Luunoronti/tercet-audio/riaa/riaa_preamp.kicad_sch

## KiCad design riaa/riaa_preamp.kicad_sch (2026-08-25)

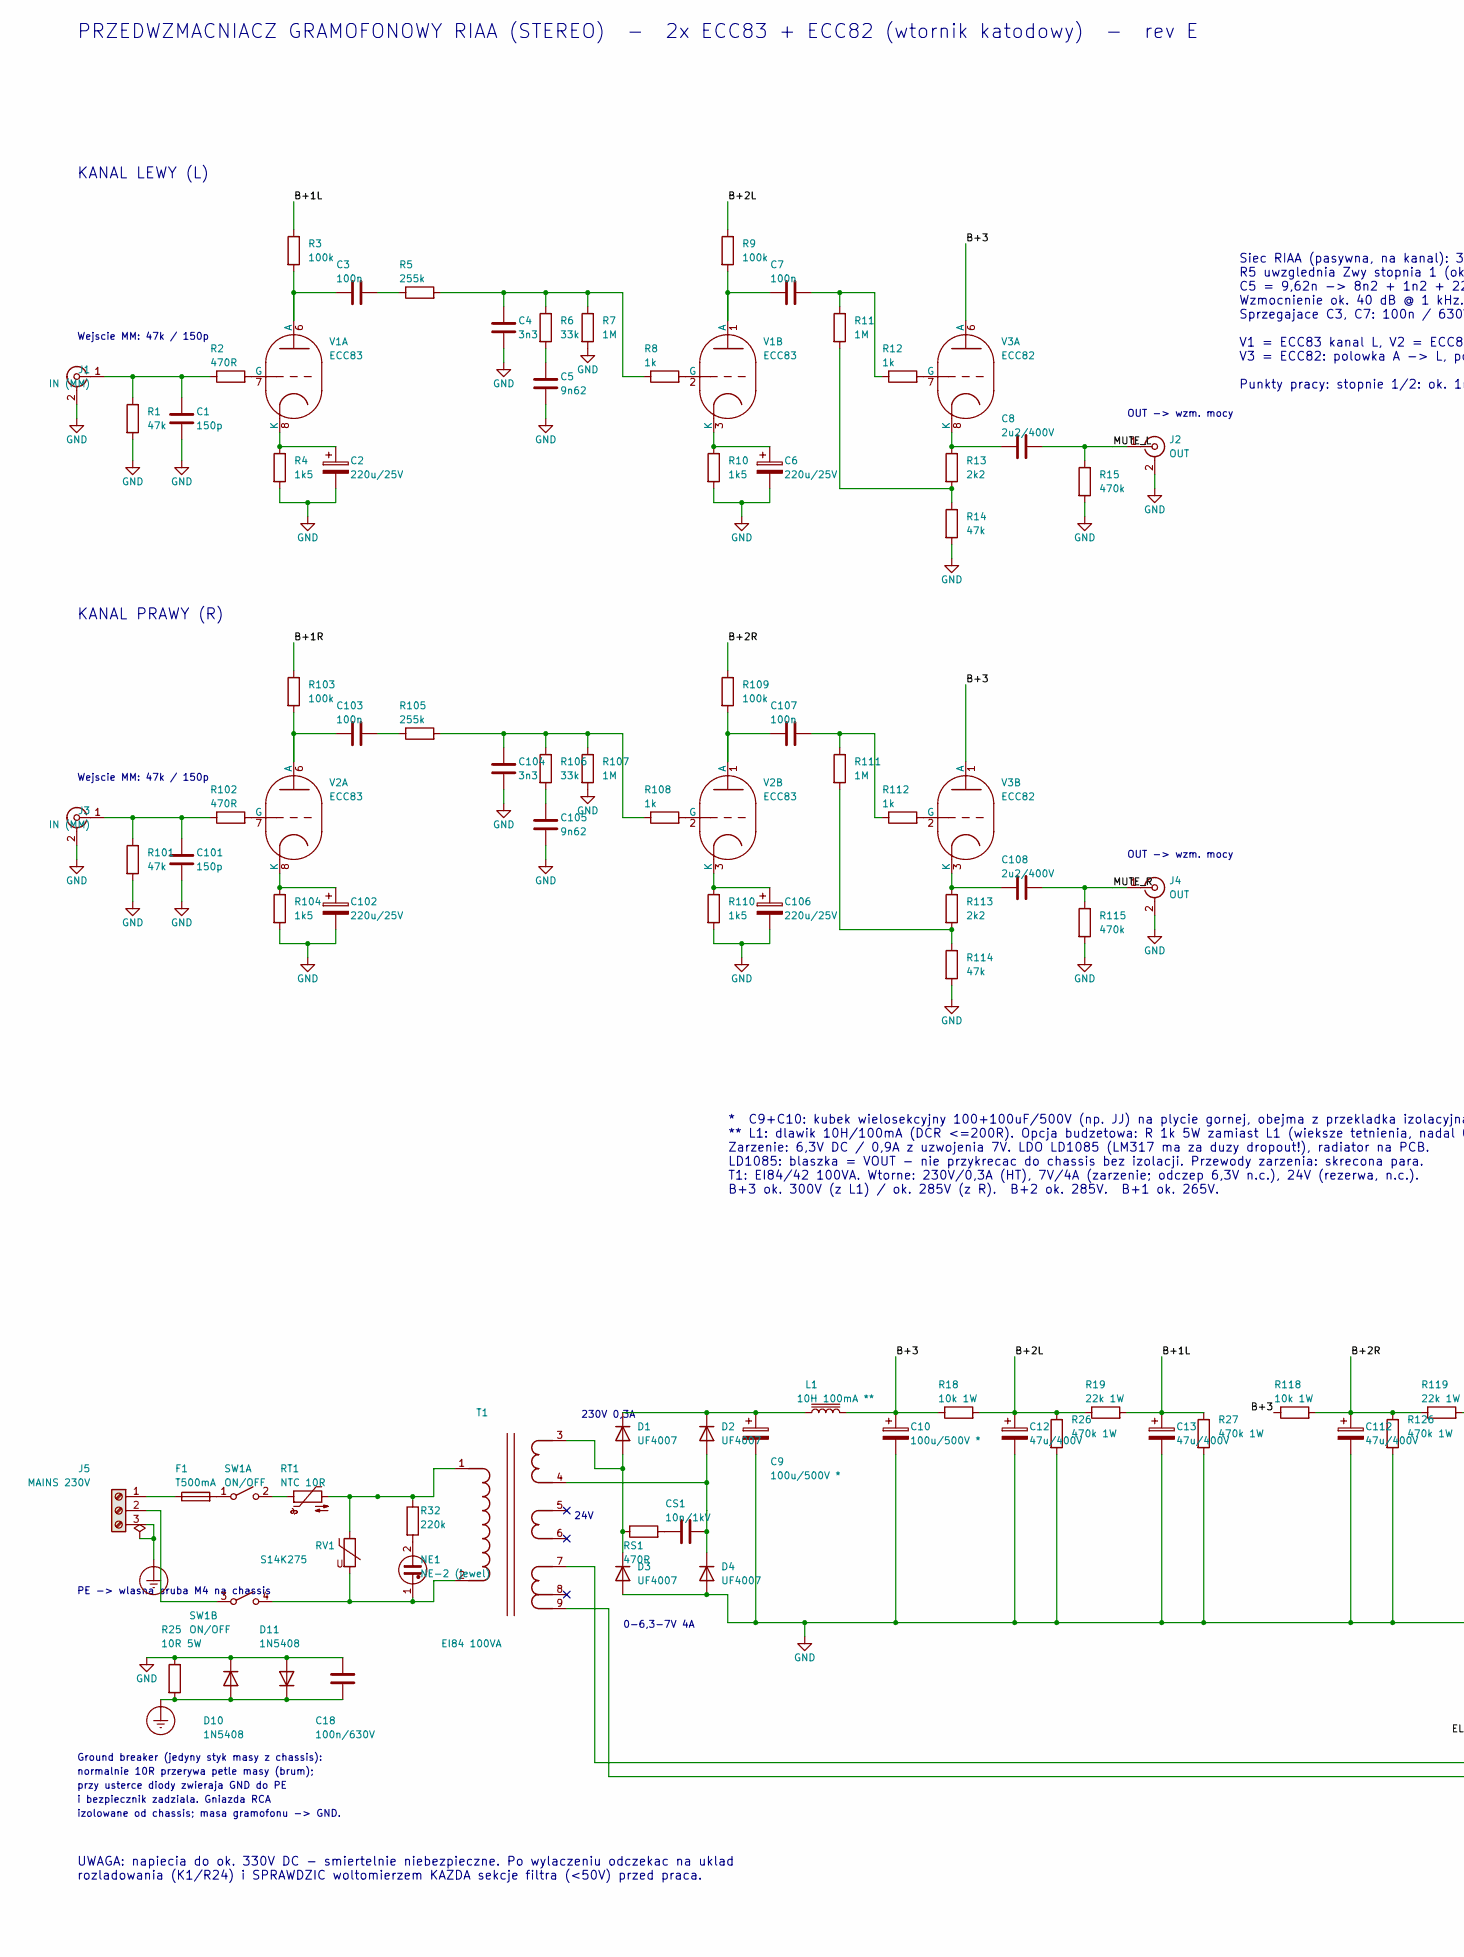
[picture p7: schematic riaa_preamp.kicad_sch, part in row 1, column 1]

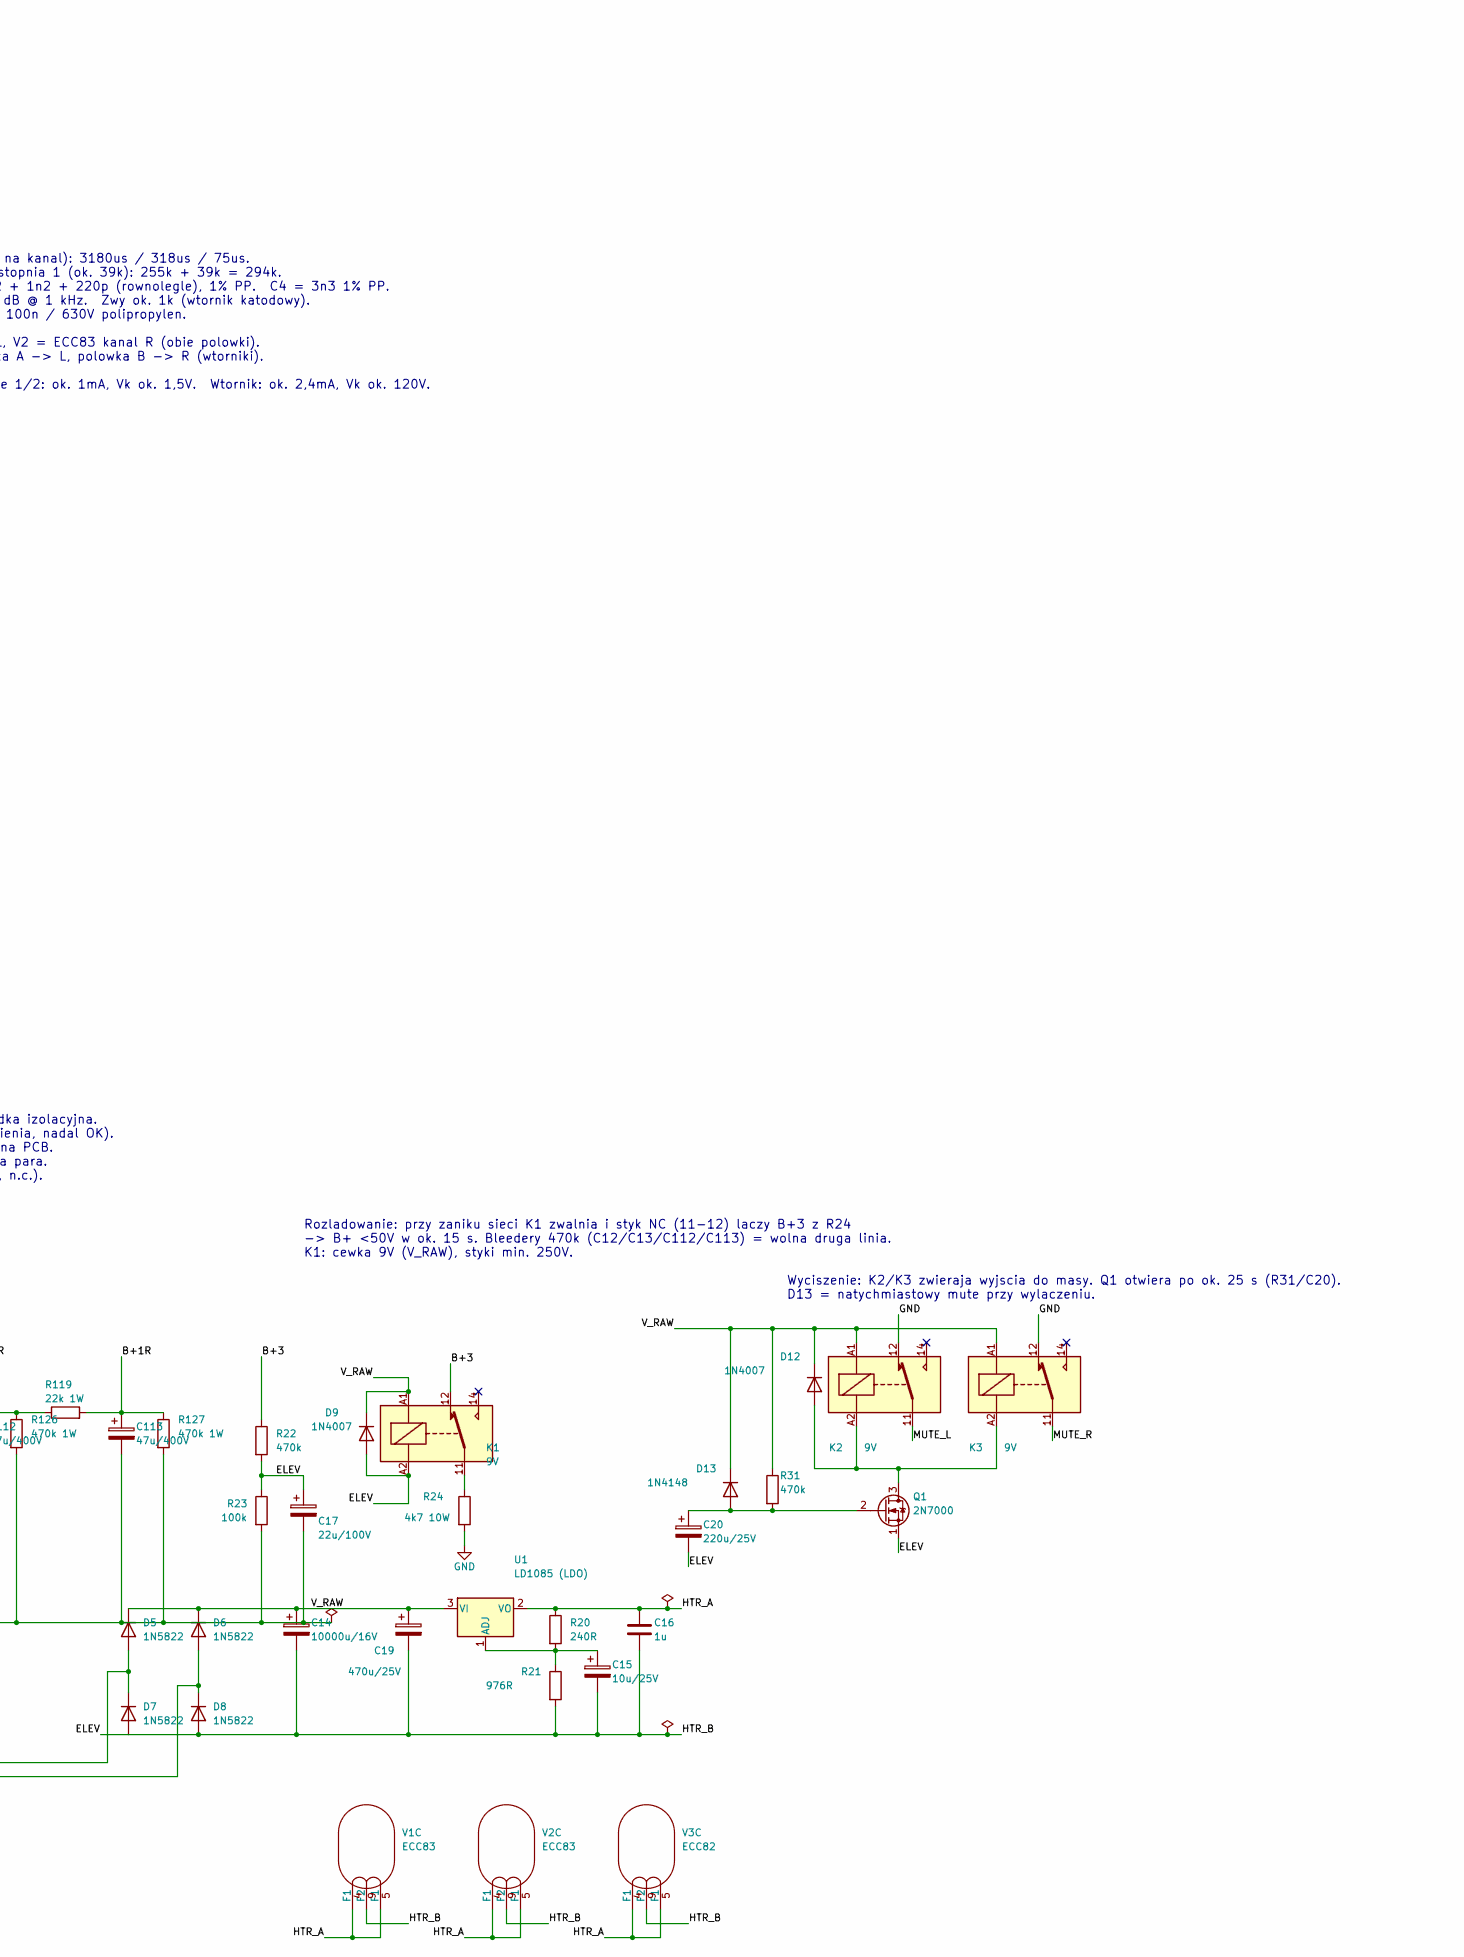
[picture p8: schematic riaa_preamp.kicad_sch, part in row 1, column 2]

Parts:
C1, C101: 150p
C2, C6, C20, C102, C106: 220u/25V
C3, C7, C103, C107: 100n
C4, C104: 3n3
C5, C105: 9n62
C8, C108: 2u2/400V
C9, C10: 100u/500V *
C12, C13, C112, C113: 47u/400V
C14: 10000u/16V
C15: 10u/25V
C16: 1u
C17: 22u/100V
C18: 100n/630V
C19: 470u/25V
CS1: 10n/1kV
D1, D2, D3, D4: UF4007
D5, D6, D7, D8: 1N5822
D9, D12: 1N4007
D10, D11: 1N5408
D13: 1N4148
F1: T500mA
J1, J3: IN (MM)
J2, J4: OUT
J5: MAINS 230V
K1, K2, K3: 9V
L1: 10H 100mA **
NE1: NE-2 (jewel)
Q1: 2N7000
R1, R14, R101, R114: 47k
R2, R102: 470R
R3, R9, R23, R103, R109: 100k
R4, R10, R104, R110: 1k5
R5, R105: 255k
R6, R106: 33k
R7, R11, R107, R111: 1M
R8, R12, R108, R112: 1k
R13, R113: 2k2
R15, R22, R31, R115: 470k
R18, R118: 10k 1W
R19, R119: 22k 1W
R20: 240R
R21: 976R
R24: 4k7 10W
R25: 10R 5W
R26, R27, R126, R127: 470k 1W
R32: 220k
RS1: 470R
RT1: NTC 10R
RV1: S14K275
SW1: ON/OFF
T1: EI84 100VA
U1: LD1085 (LDO)
V1, V2: ECC83
V3: ECC82

Connections:
B+1L: C13.1, R3.1, R19.2, R27.1
B+1R: C113.1, R103.1, R119.2, R127.1
B+2L: C12.1, R9.1, R18.2, R19.1, R26.1
B+2R: C112.1, R109.1, R118.2, R119.1, R126.1
B+3: C10.1, K1.12, L1.2, R18.1, R22.1, R118.1, V3.1 (A), V3.6 (A)
ELEV: C14.2, C15.2, C16.2, C17.1, C19.2, C20.2, D7.2 (A), D8.2 (A), D9.2 (A), K1.A2, Q1.1 (S), R21.2, R22.2, R23.1, V1.9 (F2), V2.9 (F2), V3.9 (F2)
Earth_Protective: C18.2, D10.2 (A), D11.1 (K), J5.3, R25.2
GND: C1.2, C2.2, C4.2, C5.2, C6.2, C9.2, C10.2, C12.2, C13.2, C17.2, C18.1, C101.2, C102.2, C104.2, C105.2, C106.2, C112.2, C113.2, D3.2 (A), D4.2 (A), D10.1 (K), D11.2 (A), J1.2 (Ext), J2.2 (Ext), J3.2 (Ext), J4.2 (Ext), K2.12, K3.12, R1.2, R4.2, R7.2, R10.2, R14.2, R15.2, R23.2, R24.2, R25.1, R26.2, R27.2, R101.2, R104.2, R107.2, R110.2, R114.2, R115.2, R126.2, R127.2
HTR_A: C16.1, R20.1, U1.2 (VO), V1.4 (F1), V1.5 (F1), V2.4 (F1), V2.5 (F1), V3.4 (F1), V3.5 (F1)
MUTE_L: C8.2, J2.1 (In), K2.11, R15.1
MUTE_R: C108.2, J4.1 (In), K3.11, R115.1
unnamed: C1.1, J1.1 (In), R1.1, R2.1
unnamed: C2.1, R4.1, V1.8 (K)
unnamed: C3.1, R3.2, V1.6 (A)
unnamed: C3.2, R5.1
unnamed: C4.1, R5.2, R6.1, R7.1, R8.1
unnamed: C5.1, R6.2
unnamed: C6.1, R10.1, V1.3 (K)
unnamed: C7.1, R9.2, V1.1 (A)
unnamed: C7.2, R11.1, R12.1
unnamed: C8.1, R13.1, V3.8 (K)
unnamed: C9.1, D1.1 (K), D2.1 (K), L1.1
unnamed: C15.1, R20.2, R21.1, U1.1 (ADJ)
unnamed: C20.1, D13.2 (A), Q1.2 (G), R31.2
unnamed: C101.1, J3.1 (In), R101.1, R102.1
unnamed: C102.1, R104.1, V2.8 (K)
unnamed: C103.1, R103.2, V2.6 (A)
unnamed: C103.2, R105.1
unnamed: C104.1, R105.2, R106.1, R107.1, R108.1
unnamed: C105.1, R106.2
unnamed: C106.1, R110.1, V2.3 (K)
unnamed: C107.1, R109.2, V2.1 (A)
unnamed: C107.2, R111.1, R112.1
unnamed: C108.1, R113.1, V3.3 (K)
unnamed: CS1.1, RS1.2
unnamed: CS1.2, D2.2 (A), D4.1 (K), T1.4
unnamed: D1.2 (A), D3.1 (K), RS1.1, T1.3
unnamed: D5.2 (A), D7.1 (K), T1.7
unnamed: D6.2 (A), D8.1 (K), T1.9
unnamed: D12.2 (A), K2.A2, K3.A2, Q1.3 (D)
unnamed: F1.1, J5.1
unnamed: F1.2, SW1.1 (A)
unnamed: J5.2, SW1.3 (A)
unnamed: K1.11, R24.1
unnamed: NE1.1, RV1.2, SW1.4 (B), T1.2
unnamed: NE1.2, R32.2
unnamed: R2.2, V1.7 (G)
unnamed: R8.2, V1.2 (G)
unnamed: R11.2, R13.2, R14.1
unnamed: R12.2, V3.7 (G)
unnamed: R32.1, RT1.2, RV1.1, T1.1
unnamed: R102.2, V2.7 (G)
unnamed: R108.2, V2.2 (G)
unnamed: R111.2, R113.2, R114.1
unnamed: R112.2, V3.2 (G)
unnamed: RT1.1, SW1.2 (B)
V_RAW: C14.1, C19.1, D5.1 (K), D6.1 (K), D9.1 (K), D12.1 (K), D13.1 (K), K1.A1, K2.A1, K3.A1, R31.1, U1.3 (VI)

Notes on the sheet:
KANAL LEWY (L)
Wejscie MM: 47k / 150p
OUT -> wzm. mocy
KANAL PRAWY (R)
Siec RIAA (pasywna, na kanal): 3180us / 318us / 75us.
R5 uwzglednia Zwy stopnia 1 (ok. 39k): 255k + 39k = 294k.
C5 = 9,62n -> 8n2 + 1n2 + 220p (rownolegle), 1% PP. C4 = 3n3 1% PP.
Wzmocnienie ok. 40 dB @ 1 kHz. Zwy ok. 1k (wtornik katodowy).
Sprzegajace C3, C7: 100n / 630V polipropylen.
V1 = ECC83 kanal L, V2 = ECC83 kanal R (obie polowki).
V3 = ECC82: polowka A -> L, polowka B -> R (wtorniki).
Punkty pracy: stopnie 1/2: ok. 1mA, Vk ok. 1,5V. Wtornik: ok. 2,4mA, Vk ok. 120V.
PE -> wlasna sruba M4 na chassis
230V 0,3A
24V
0-6,3-7V 4A
Rozladowanie: przy zaniku sieci K1 zwalnia i styk NC (11-12) laczy B+3 z R24
-> B+ <50V w ok. 15 s. Bleedery 470k (C12/C13/C112/C113) = wolna druga linia.
K1: cewka 9V (V_RAW), styki min. 250V.
Wyciszenie: K2/K3 zwieraja wyjscia do masy. Q1 otwiera po ok. 25 s (R31/C20).
D13 = natychmiastowy mute przy wylaczeniu.
Ground breaker (jedyny styk masy z chassis):
normalnie 10R przerywa petle masy (brum);
przy usterce diody zwieraja GND do PE
i bezpiecznik zadziala. Gniazda RCA
izolowane od chassis; masa gramofonu -> GND.
PRZEDWZMACNIACZ GRAMOFONOWY RIAA (STEREO) - 2x ECC83 + ECC82 (wtornik katodowy) - rev E
* C9+C10: kubek wielosekcyjny 100+100uF/500V (np. JJ) na plycie gornej, obejma z przekladka izolacyjna.
** L1: dlawik 10H/100mA (DCR <=200R). Opcja budzetowa: R 1k 5W zamiast L1 (wieksze tetnienia, nadal OK).
Zarzenie: 6,3V DC / 0,9A z uzwojenia 7V. LDO LD1085 (LM317 ma za duzy dropout!), radiator na PCB.
LD1085: blaszka = VOUT - nie przykrecac do chassis bez izolacji. Przewody zarzenia: skrecona para.
T1: EI84/42 100VA. Wtorne: 230V/0,3A (HT), 7V/4A (zarzenie; odczep 6,3V n.c.), 24V (rezerwa, n.c.).
B+3 ok. 300V (z L1) / ok. 285V (z R). B+2 ok. 285V. B+1 ok. 265V.
UWAGA: napiecia do ok. 330V DC - smiertelnie niebezpieczne. Po wylaczeniu odczekac na uklad
rozladowania (K1/R24) i SPRAWDZIC woltomierzem KAZDA sekcje filtra (<50V) przed praca.
