Luunoronti/tercet-audio/riaa/riaa_preamp_purist.kicad_sch

## KiCad design riaa/riaa_preamp_purist.kicad_sch (2026-08-26)

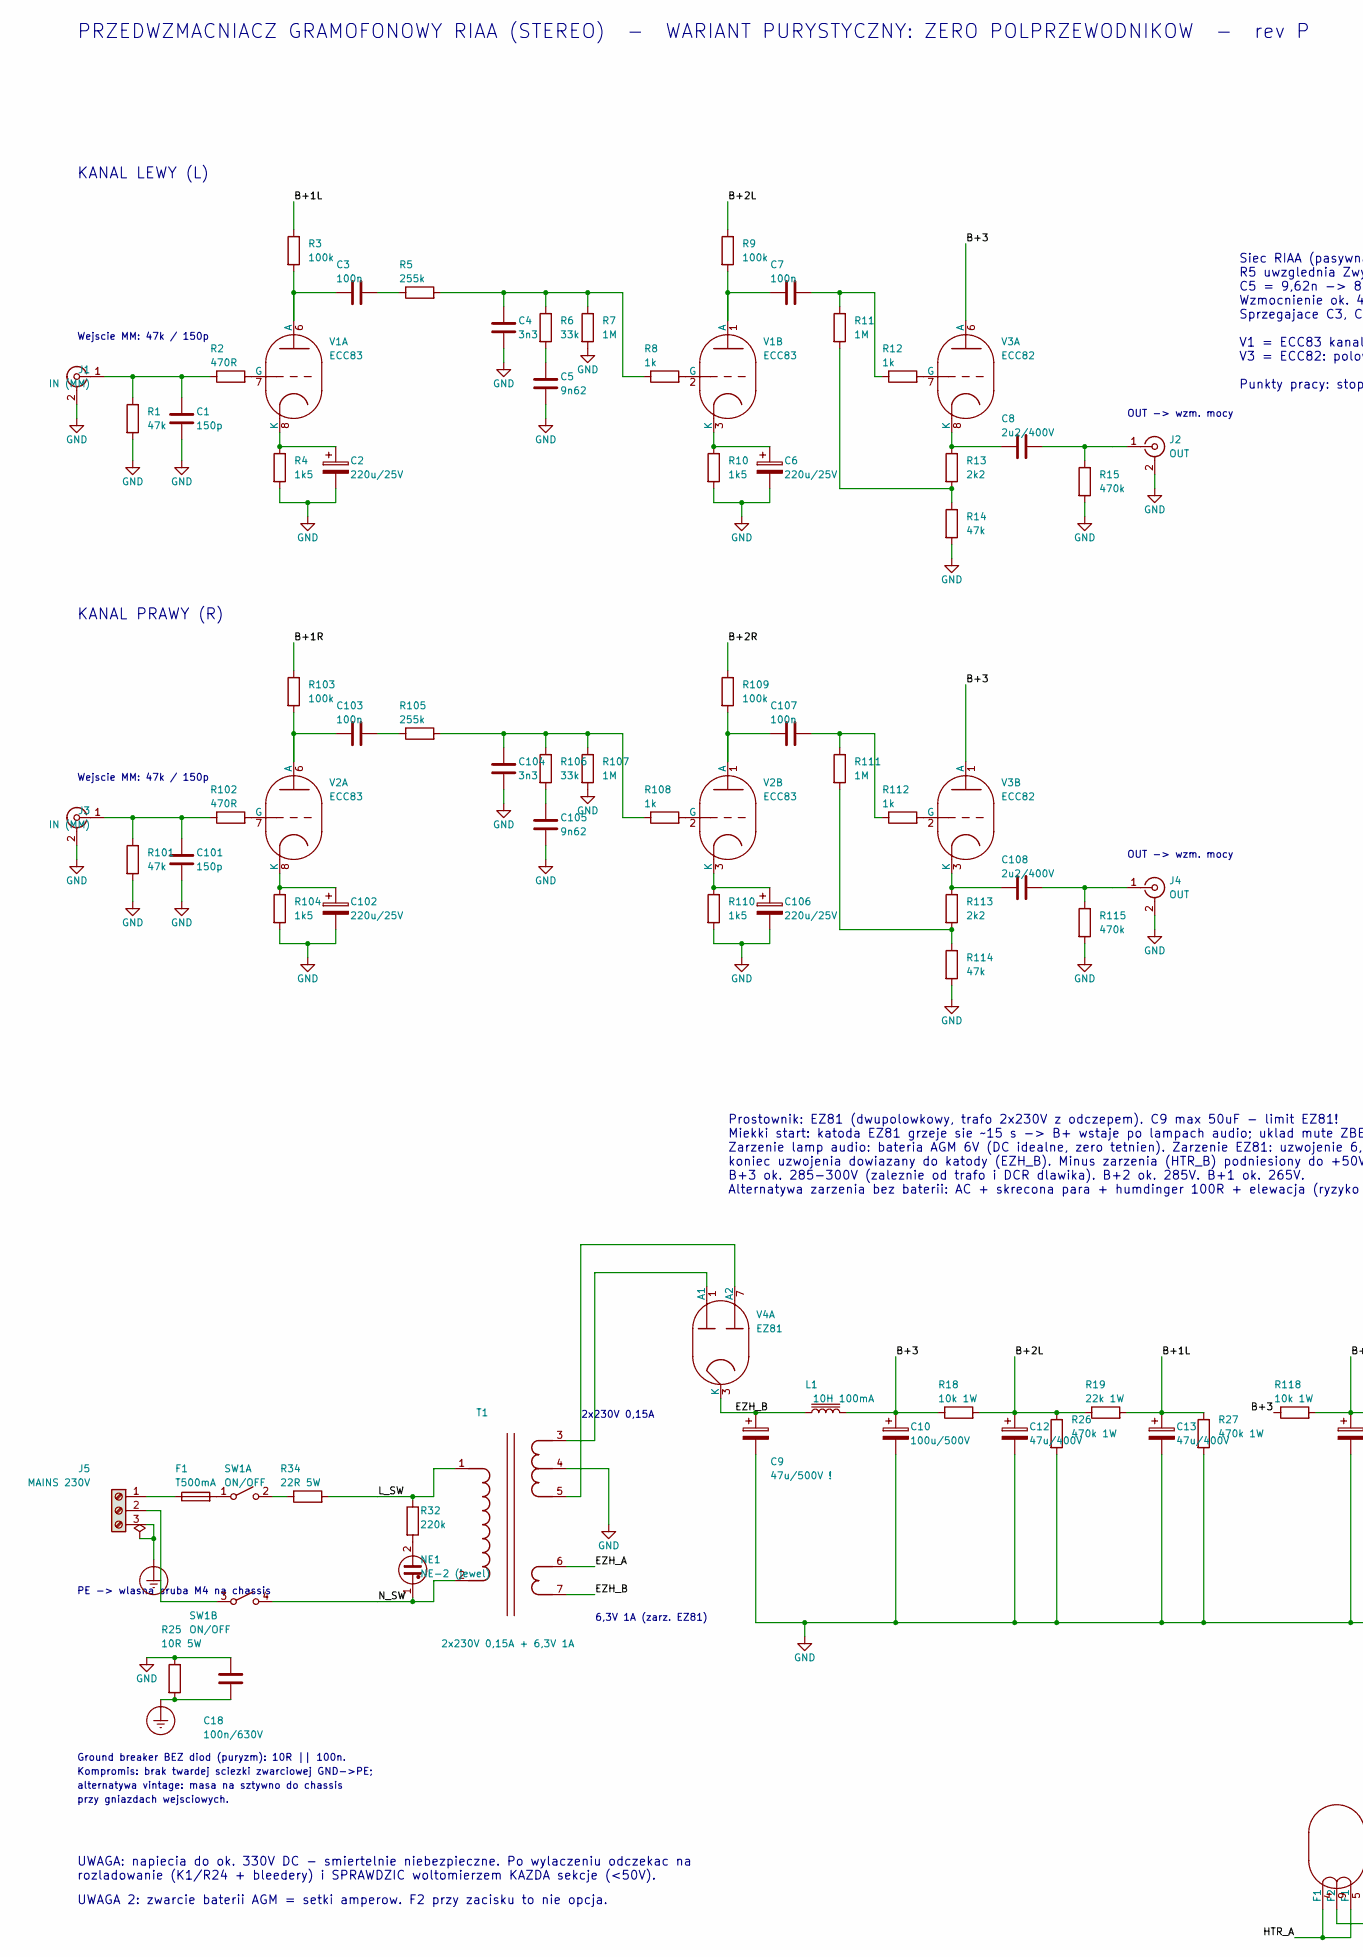
[picture p9: schematic riaa_preamp_purist.kicad_sch, part in row 1, column 1]

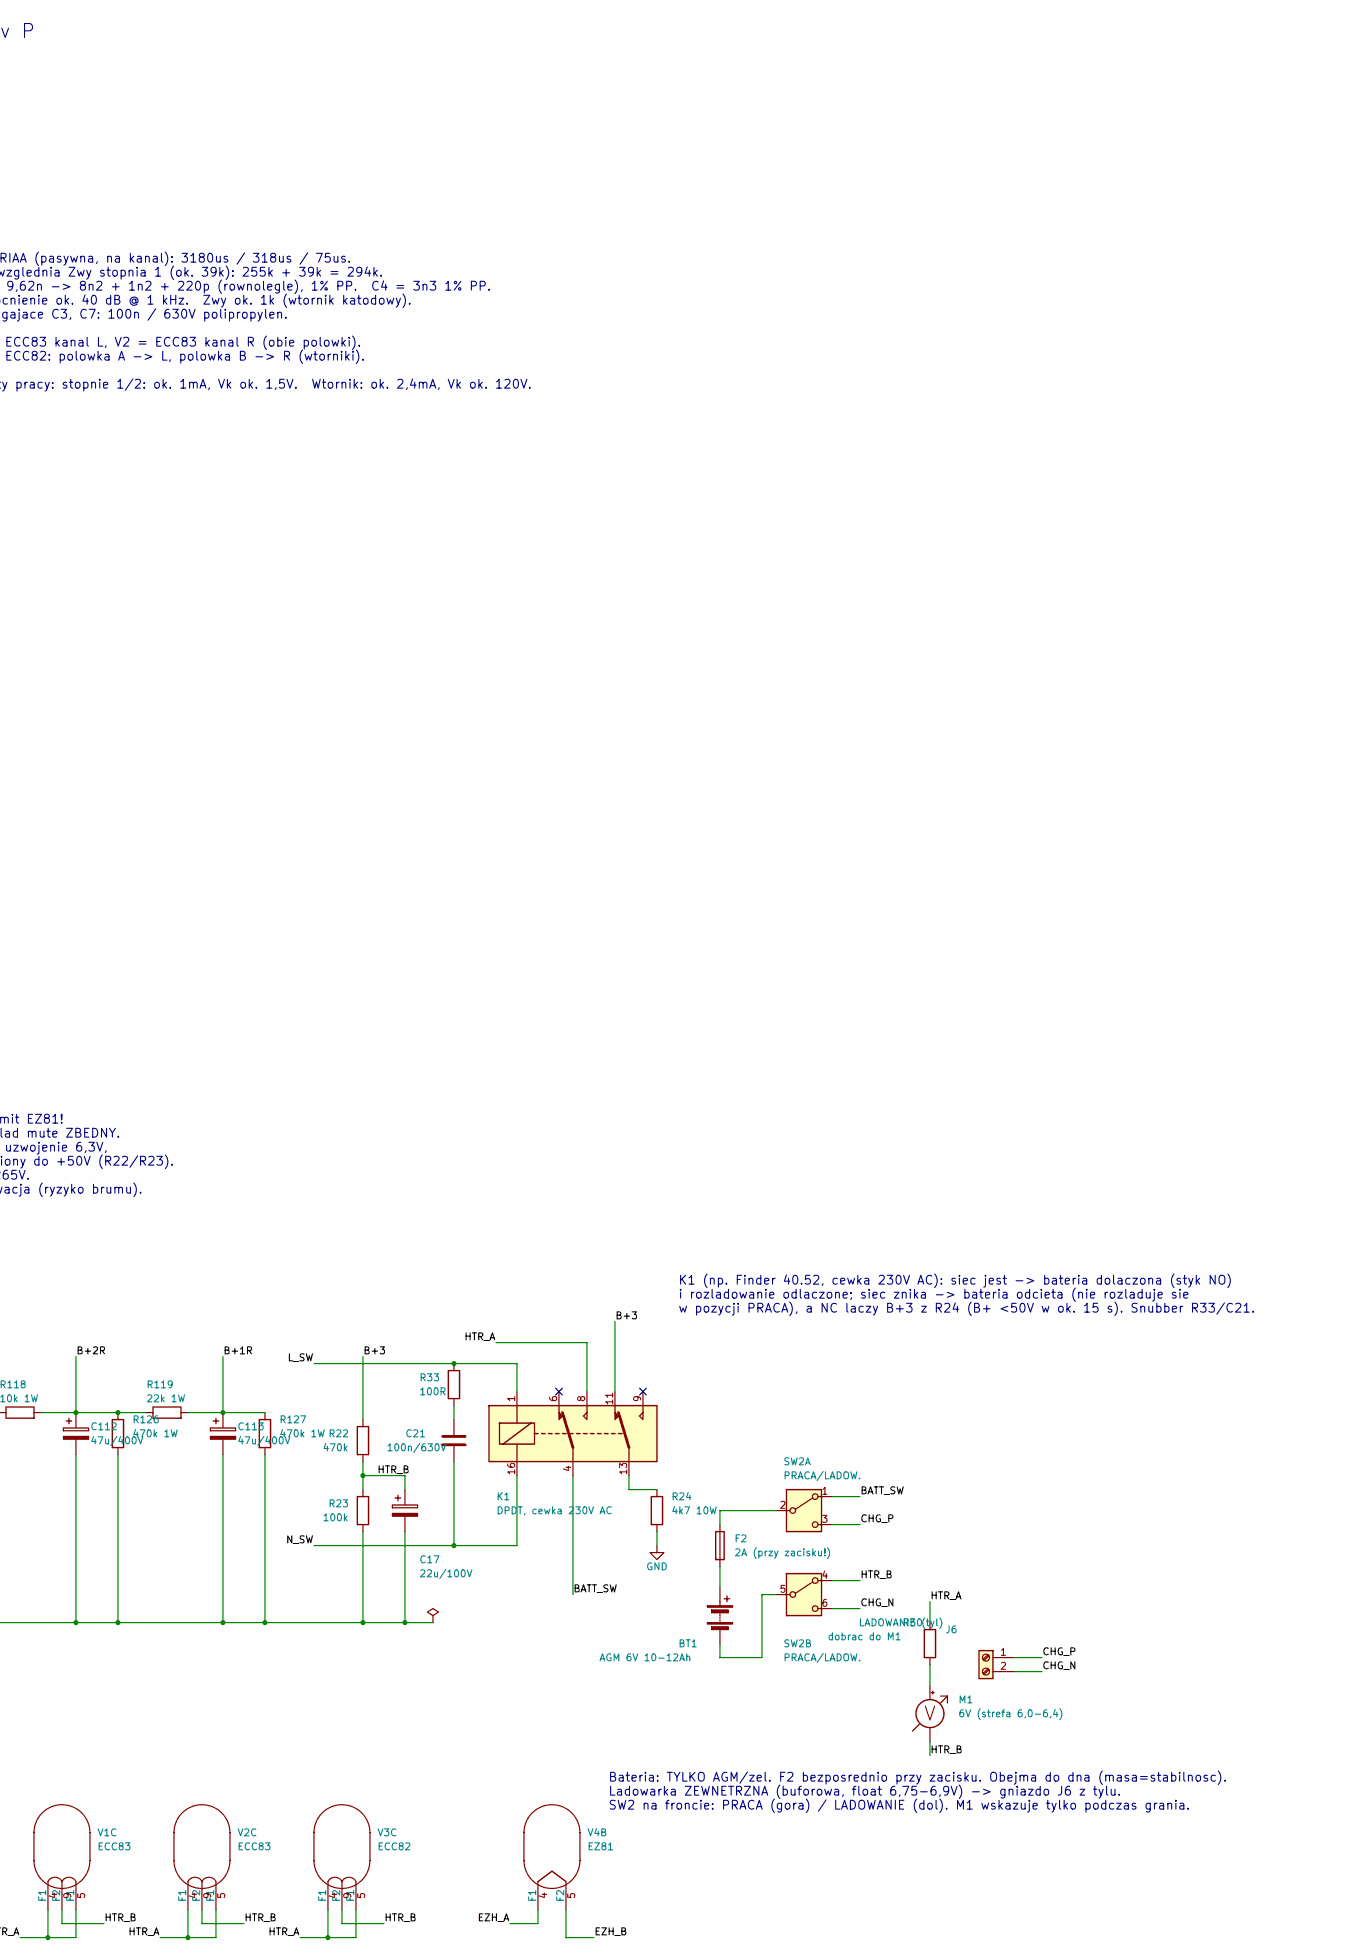
[picture p10: schematic riaa_preamp_purist.kicad_sch, part in row 1, column 2]

Parts:
BT1: AGM 6V 10-12Ah
C1, C101: 150p
C2, C6, C102, C106: 220u/25V
C3, C7, C103, C107: 100n
C4, C104: 3n3
C5, C105: 9n62
C8, C108: 2u2/400V
C9: 47u/500V !
C10: 100u/500V
C12, C13, C112, C113: 47u/400V
C17: 22u/100V
C18, C21: 100n/630V
F1: T500mA
F2: 2A (przy zacisku!)
J1, J3: IN (MM)
J2, J4: OUT
J5: MAINS 230V
J6: LADOWANIE (tyl)
K1: DPDT, cewka 230V AC
L1: 10H 100mA
M1: 6V (strefa 6,0-6,4)
NE1: NE-2 (jewel)
R1, R14, R101, R114: 47k
R2, R102: 470R
R3, R9, R23, R103, R109: 100k
R4, R10, R104, R110: 1k5
R5, R105: 255k
R6, R106: 33k
R7, R11, R107, R111: 1M
R8, R12, R108, R112: 1k
R13, R113: 2k2
R15, R22, R115: 470k
R18, R118: 10k 1W
R19, R119: 22k 1W
R24: 4k7 10W
R25: 10R 5W
R26, R27, R126, R127: 470k 1W
R30: dobrac do M1
R32: 220k
R33: 100R
R34: 22R 5W
SW1: ON/OFF
SW2: PRACA/LADOW.
T1: 2x230V 0,15A + 6,3V 1A
V1, V2: ECC83
V3: ECC82
V4: EZ81

Connections:
B+1L: C13.1, R3.1, R19.2, R27.1
B+1R: C113.1, R103.1, R119.2, R127.1
B+2L: C12.1, R9.1, R18.2, R19.1, R26.1
B+2R: C112.1, R109.1, R118.2, R119.1, R126.1
B+3: C10.1, K1.11, L1.2, R18.1, R22.1, R118.1, V3.1 (A), V3.6 (A)
BATT_SW: K1.4, SW2.1 (A)
CHG_N: J6.2, SW2.6 (C)
CHG_P: J6.1, SW2.3 (C)
EZH_A: T1.6, V4.4 (F1)
EZH_B: C9.1, L1.1, T1.7, V4.3 (K), V4.5 (F2)
Earth_Protective: C18.2, J5.3, R25.2
GND: C1.2, C2.2, C4.2, C5.2, C6.2, C9.2, C10.2, C12.2, C13.2, C17.2, C18.1, C101.2, C102.2, C104.2, C105.2, C106.2, C112.2, C113.2, J1.2 (Ext), J2.2 (Ext), J3.2 (Ext), J4.2 (Ext), R1.2, R4.2, R7.2, R10.2, R14.2, R15.2, R23.2, R24.2, R25.1, R26.2, R27.2, R101.2, R104.2, R107.2, R110.2, R114.2, R115.2, R126.2, R127.2, T1.4
HTR_A: K1.8, R30.1, V1.4 (F1), V1.5 (F1), V2.4 (F1), V2.5 (F1), V3.4 (F1), V3.5 (F1)
HTR_B: C17.1, M1.1 (-), R22.2, R23.1, SW2.4 (A), V1.9 (F2), V2.9 (F2), V3.9 (F2)
L_SW: K1.1, R32.1, R33.1, R34.2, T1.1
N_SW: C21.2, K1.16, NE1.1, SW1.4 (B), T1.2
unnamed: BT1.1 (+), F2.2
unnamed: BT1.2 (-), SW2.5 (B)
unnamed: C1.1, J1.1 (In), R1.1, R2.1
unnamed: C2.1, R4.1, V1.8 (K)
unnamed: C3.1, R3.2, V1.6 (A)
unnamed: C3.2, R5.1
unnamed: C4.1, R5.2, R6.1, R7.1, R8.1
unnamed: C5.1, R6.2
unnamed: C6.1, R10.1, V1.3 (K)
unnamed: C7.1, R9.2, V1.1 (A)
unnamed: C7.2, R11.1, R12.1
unnamed: C8.1, R13.1, V3.8 (K)
unnamed: C8.2, J2.1 (In), R15.1
unnamed: C21.1, R33.2
unnamed: C101.1, J3.1 (In), R101.1, R102.1
unnamed: C102.1, R104.1, V2.8 (K)
unnamed: C103.1, R103.2, V2.6 (A)
unnamed: C103.2, R105.1
unnamed: C104.1, R105.2, R106.1, R107.1, R108.1
unnamed: C105.1, R106.2
unnamed: C106.1, R110.1, V2.3 (K)
unnamed: C107.1, R109.2, V2.1 (A)
unnamed: C107.2, R111.1, R112.1
unnamed: C108.1, R113.1, V3.3 (K)
unnamed: C108.2, J4.1 (In), R115.1
unnamed: F1.1, J5.1
unnamed: F1.2, SW1.1 (A)
unnamed: F2.1, SW2.2 (B)
unnamed: J5.2, SW1.3 (A)
unnamed: K1.13, R24.1
unnamed: M1.2 (+), R30.2
unnamed: NE1.2, R32.2
unnamed: R2.2, V1.7 (G)
unnamed: R8.2, V1.2 (G)
unnamed: R11.2, R13.2, R14.1
unnamed: R12.2, V3.7 (G)
unnamed: R34.1, SW1.2 (B)
unnamed: R102.2, V2.7 (G)
unnamed: R108.2, V2.2 (G)
unnamed: R111.2, R113.2, R114.1
unnamed: R112.2, V3.2 (G)
unnamed: T1.3, V4.1 (A1)
unnamed: T1.5, V4.7 (A2)

Notes on the sheet:
KANAL LEWY (L)
Wejscie MM: 47k / 150p
OUT -> wzm. mocy
KANAL PRAWY (R)
Siec RIAA (pasywna, na kanal): 3180us / 318us / 75us.
R5 uwzglednia Zwy stopnia 1 (ok. 39k): 255k + 39k = 294k.
C5 = 9,62n -> 8n2 + 1n2 + 220p (rownolegle), 1% PP. C4 = 3n3 1% PP.
Wzmocnienie ok. 40 dB @ 1 kHz. Zwy ok. 1k (wtornik katodowy).
Sprzegajace C3, C7: 100n / 630V polipropylen.
V1 = ECC83 kanal L, V2 = ECC83 kanal R (obie polowki).
V3 = ECC82: polowka A -> L, polowka B -> R (wtorniki).
Punkty pracy: stopnie 1/2: ok. 1mA, Vk ok. 1,5V. Wtornik: ok. 2,4mA, Vk ok. 120V.
PE -> wlasna sruba M4 na chassis
2x230V 0,15A
6,3V 1A (zarz. EZ81)
K1 (np. Finder 40.52, cewka 230V AC): siec jest -> bateria dolaczona (styk NO)
i rozladowanie odlaczone; siec znika -> bateria odcieta (nie rozladuje sie
w pozycji PRACA), a NC laczy B+3 z R24 (B+ <50V w ok. 15 s). Snubber R33/C21.
Bateria: TYLKO AGM/zel. F2 bezposrednio przy zacisku. Obejma do dna (masa=stabilnosc).
Ladowarka ZEWNETRZNA (buforowa, float 6,75-6,9V) -> gniazdo J6 z tylu.
SW2 na froncie: PRACA (gora) / LADOWANIE (dol). M1 wskazuje tylko podczas grania.
Ground breaker BEZ diod (puryzm): 10R || 100n.
Kompromis: brak twardej sciezki zwarciowej GND->PE;
alternatywa vintage: masa na sztywno do chassis
przy gniazdach wejsciowych.
PRZEDWZMACNIACZ GRAMOFONOWY RIAA (STEREO) - WARIANT PURYSTYCZNY: ZERO POLPRZEWODNIKOW - rev P
Prostownik: EZ81 (dwupolowkowy, trafo 2x230V z odczepem). C9 max 50uF - limit EZ81!
Miekki start: katoda EZ81 grzeje sie ~15 s -> B+ wstaje po lampach audio; uklad mute ZBEDNY.
Zarzenie lamp audio: bateria AGM 6V (DC idealne, zero tetnien). Zarzenie EZ81: uzwojenie 6,3V,
koniec uzwojenia dowiazany do katody (EZH_B). Minus zarzenia (HTR_B) podniesiony do +50V (R22/R23).
B+3 ok. 285-300V (zaleznie od trafo i DCR dlawika). B+2 ok. 285V. B+1 ok. 265V.
Alternatywa zarzenia bez baterii: AC + skrecona para + humdinger 100R + elewacja (ryzyko brumu).
UWAGA: napiecia do ok. 330V DC - smiertelnie niebezpieczne. Po wylaczeniu odczekac na
rozladowanie (K1/R24 + bleedery) i SPRAWDZIC woltomierzem KAZDA sekcje (<50V).
UWAGA 2: zwarcie baterii AGM = setki amperow. F2 przy zacisku to nie opcja.
