Luunoronti/tercet-audio/headamp/kicad/headamp.kicad_sch

## KiCad design headamp/kicad/headamp.kicad_sch (2026-09-08)

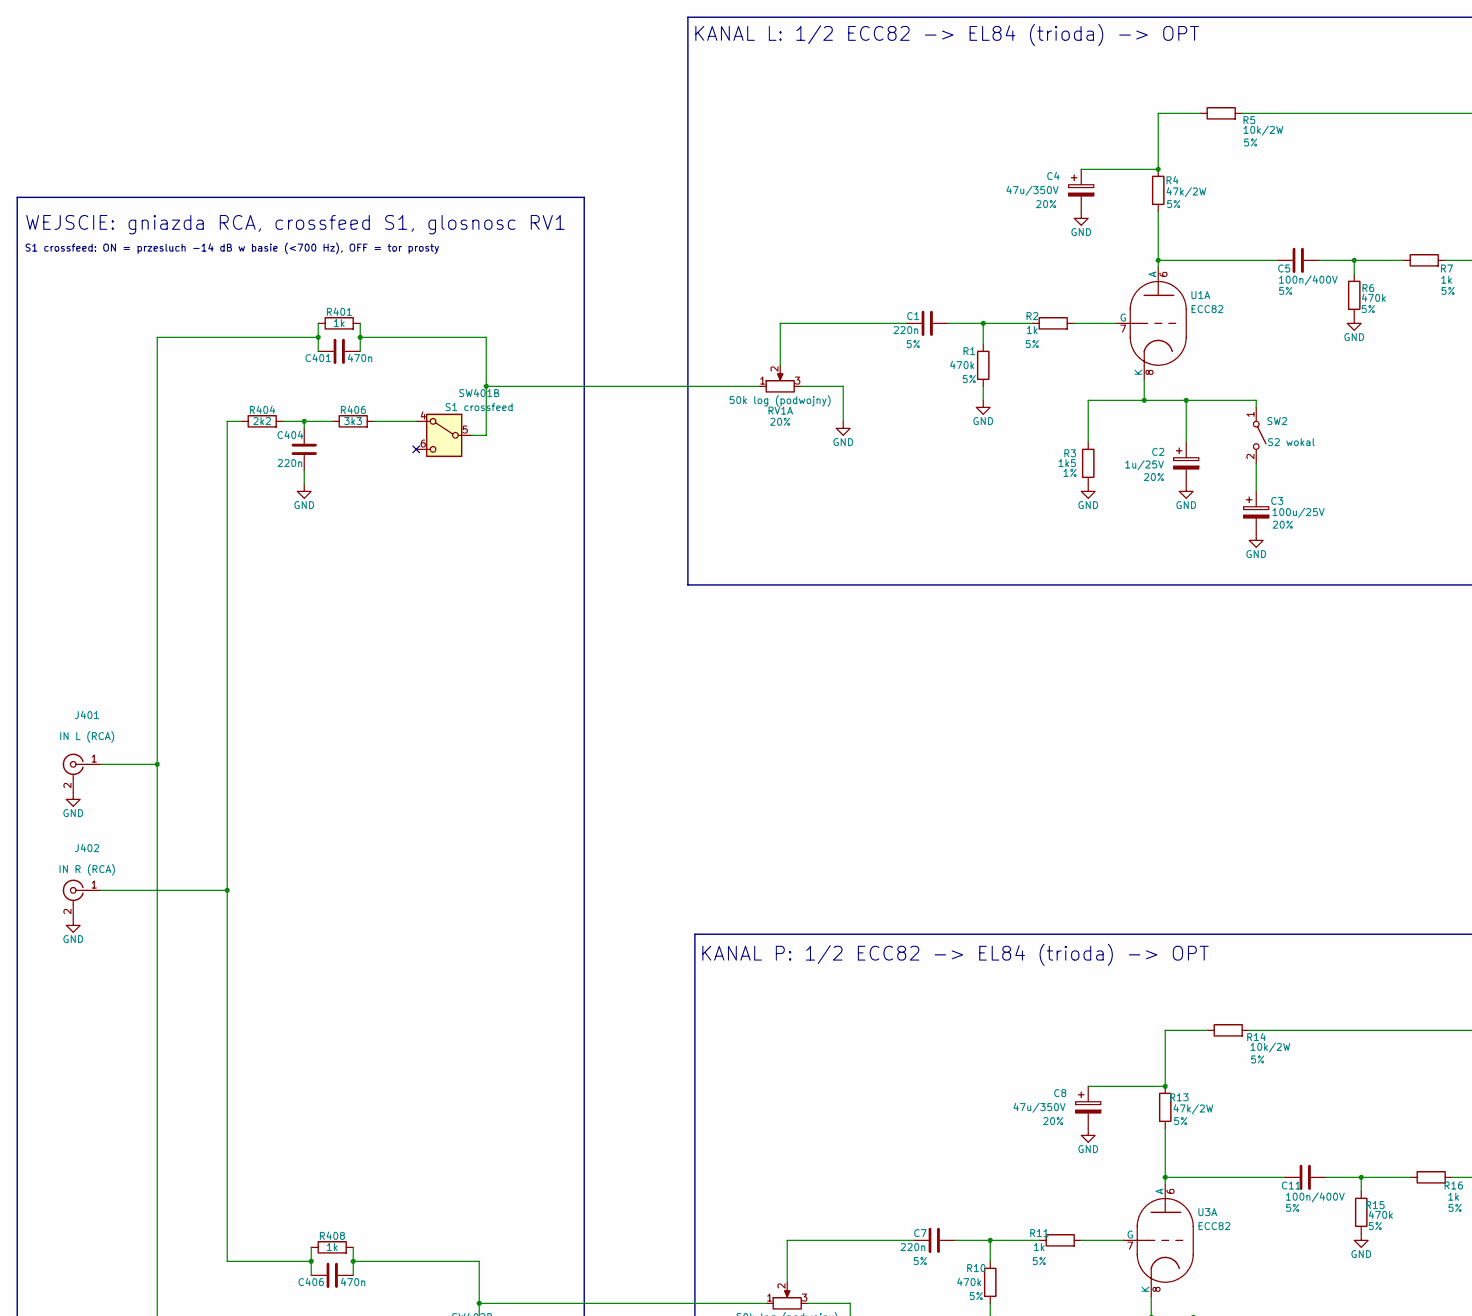
[picture p11: schematic headamp.kicad_sch, part in row 1, column 1]

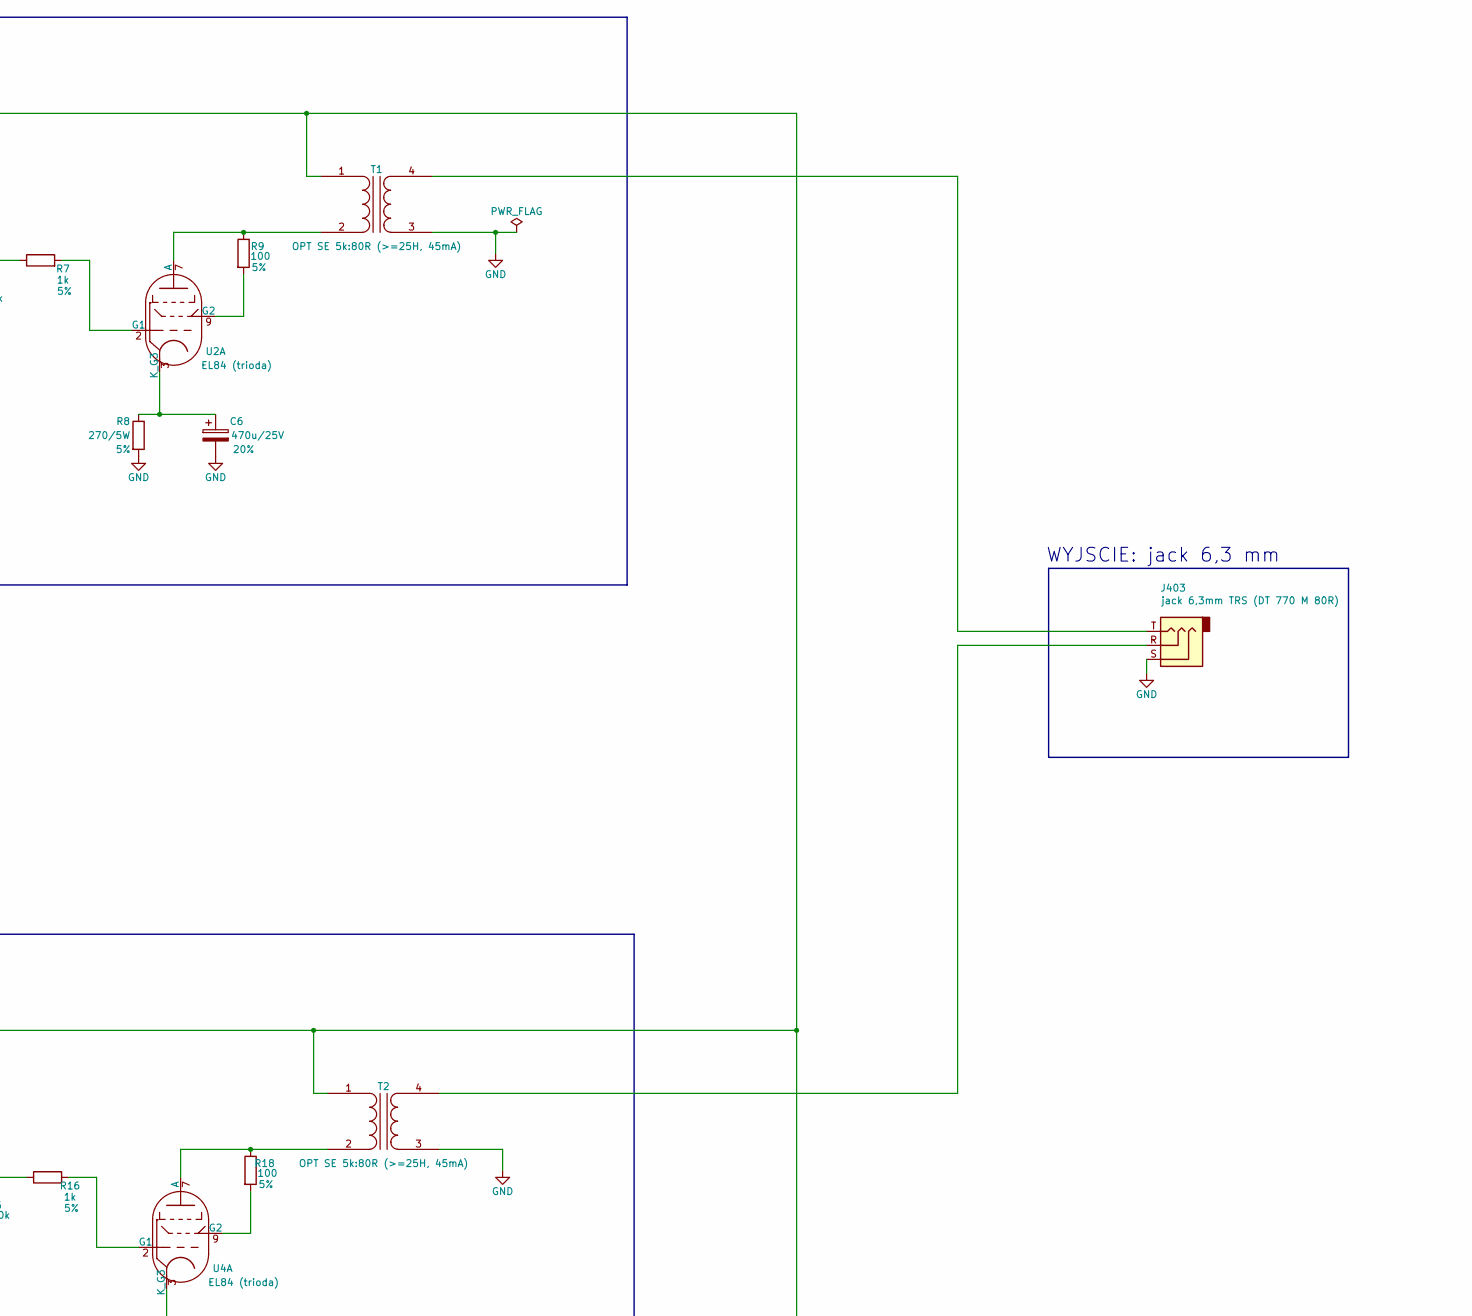
[picture p12: schematic headamp.kicad_sch, part in row 1, column 2]

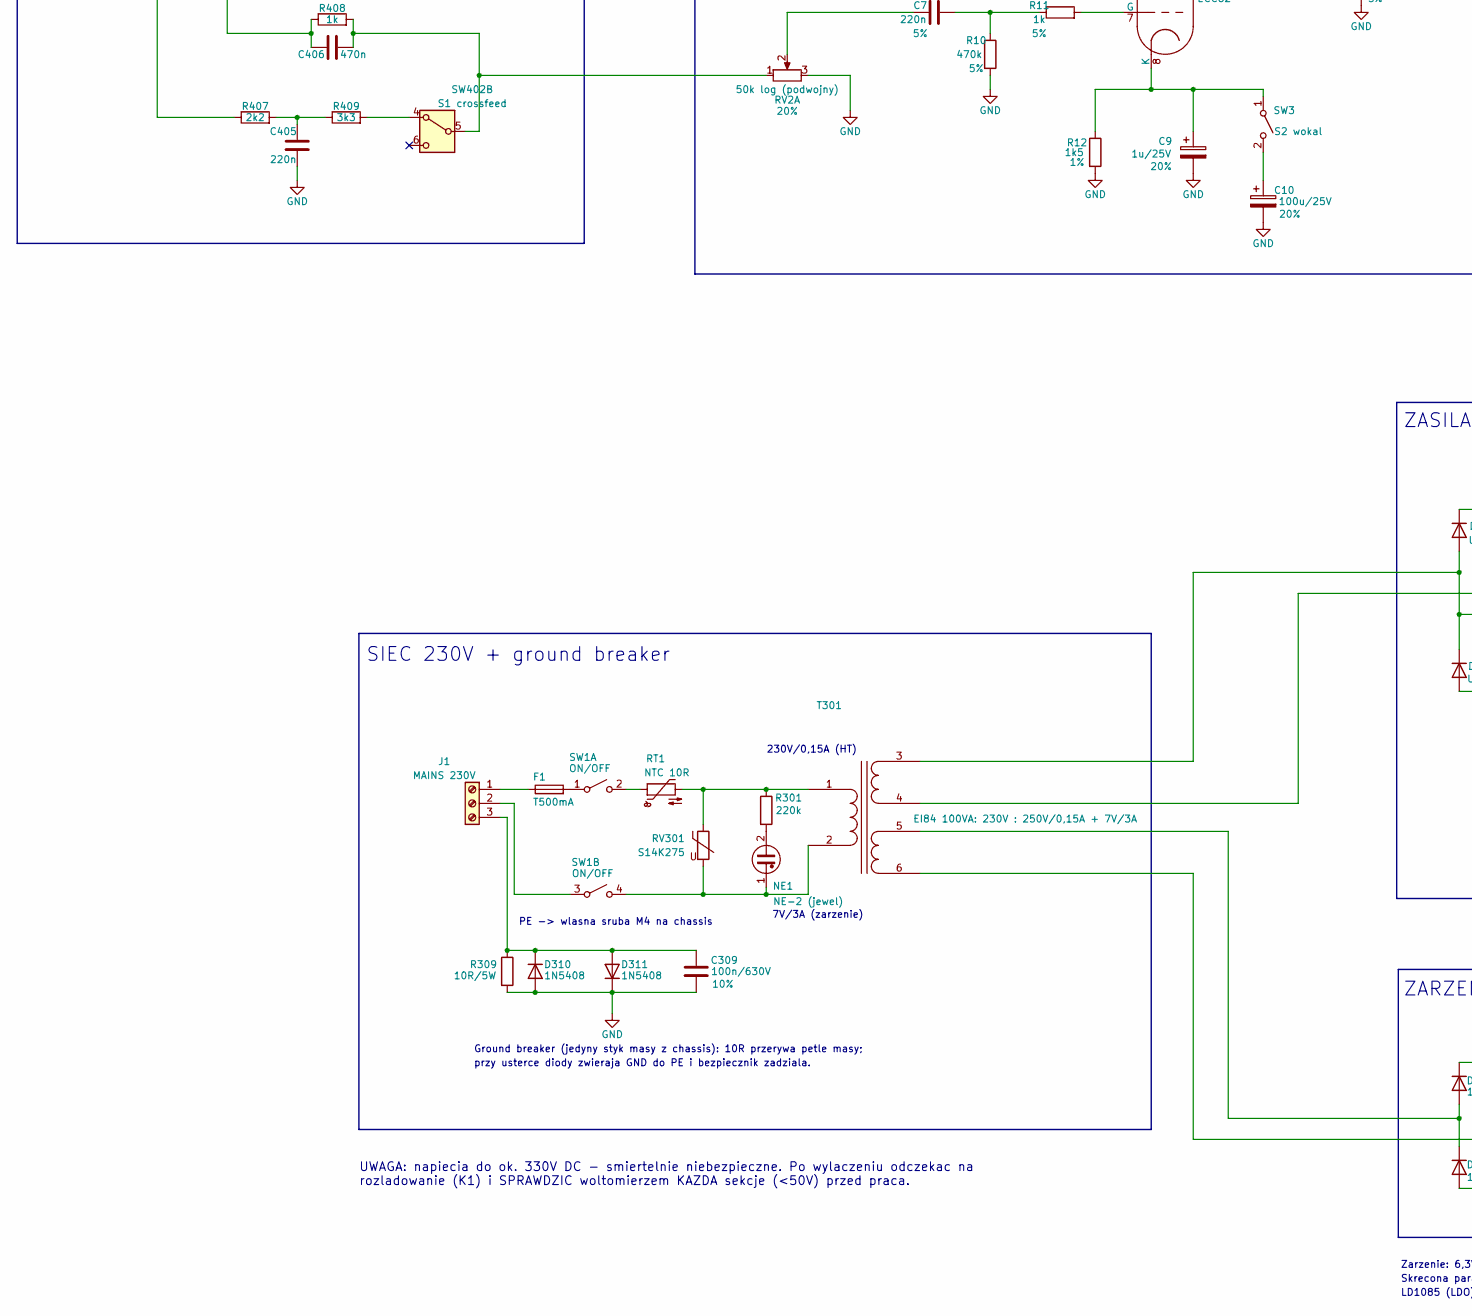
[picture p13: schematic headamp.kicad_sch, part in row 2, column 1]

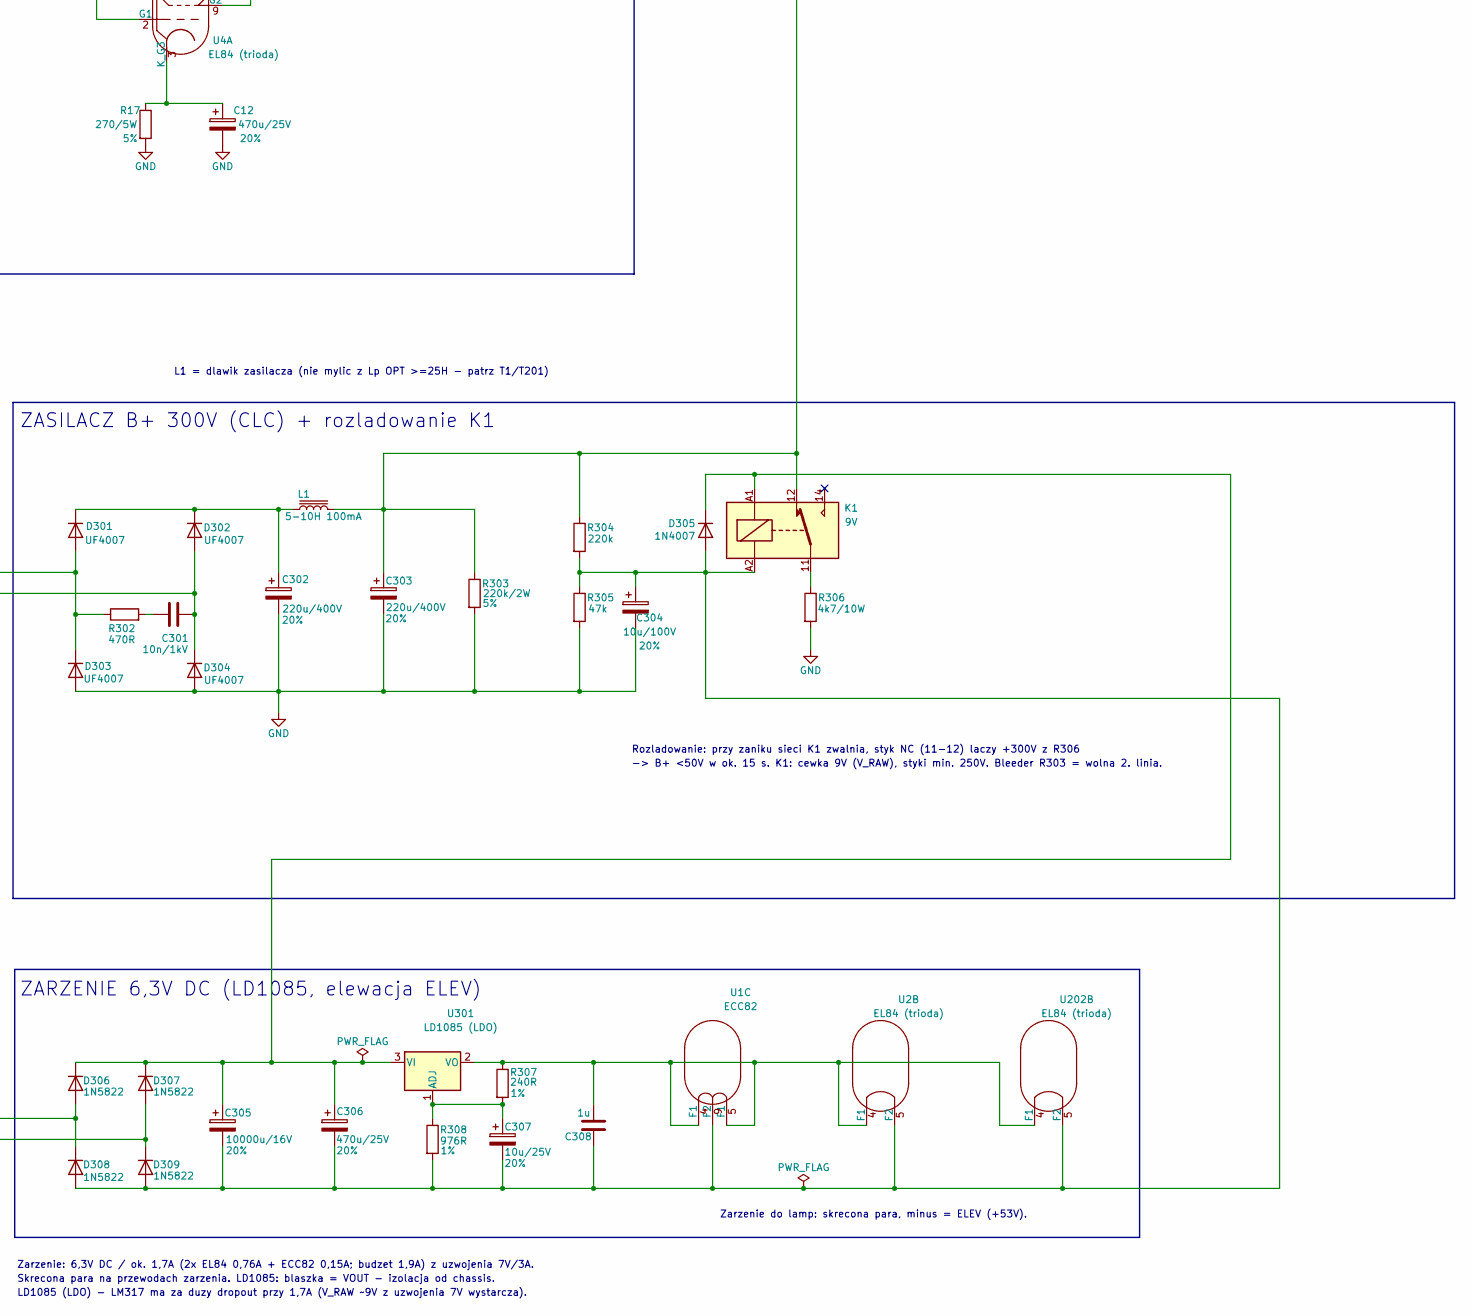
[picture p14: schematic headamp.kicad_sch, part in row 2, column 2]

Parts:
C1, C7: 220n; Tolerance 5%
C2, C9: 1u/25V; Tolerance 20%
C3, C10: 100u/25V; Tolerance 20%
C4, C8: 47u/350V; Tolerance 20%
C5, C11: 100n/400V; Tolerance 5%
C6, C12, C306: 470u/25V; Tolerance 20%
C301: 10n/1kV
C302, C303: 220u/400V; Tolerance 20%
C304: 10u/100V; Tolerance 20%
C305: 10000u/16V; Tolerance 20%
C307: 10u/25V; Tolerance 20%
C308: 1u
C309: 100n/630V; Tolerance 10%
C401, C406: 470n
C404, C405: 220n
D301, D302, D303, D304: UF4007
D305: 1N4007
D306, D307, D308, D309: 1N5822
D310, D311: 1N5408
F1: T500mA
J1: MAINS 230V
J401: IN L (RCA)
J402: IN R (RCA)
J403: jack 6,3mm TRS (DT 770 M 80R)
K1: 9V
L1: 5-10H 100mA
NE1: NE-2 (jewel)
R1, R6, R10, R15: 470k; Tolerance 5%
R2, R7, R11, R16: 1k; Tolerance 5%
R3, R12: 1k5; Tolerance 1%
R4, R13: 47k/2W; Tolerance 5%
R5, R14: 10k/2W; Tolerance 5%
R8, R17: 270/5W; Tolerance 5%
R9, R18: 100; Tolerance 5%
R301, R304: 220k
R302: 470R
R303: 220k/2W; Tolerance 5%
R305: 47k
R306: 4k7/10W
R307: 240R; Tolerance 1%
R308: 976R; Tolerance 1%
R309: 10R/5W
R401, R408: 1k
R404, R407: 2k2
R406, R409: 3k3
RT1: NTC 10R
RV1, RV2: 50k log (podwojny); Tolerance 20%
RV301: S14K275
SW1: ON/OFF
SW2, SW3: S2 wokal
SW401, SW402: S1 crossfeed
T1, T2: OPT SE 5k:80R (>=25H, 45mA)
T301: EI84 100VA: 230V : 250V/0,15A + 7V/3A
U1, U3: ECC82
U2, U4, U202: EL84 (trioda)
U301: LD1085 (LDO)

Connections:
GND: C2.2, C3.2, C4.2, C6.2, C8.2, C9.2, C10.2, C12.2, C302.2, C303.2, C304.2, C309.2, C404.1, C405.1, D303.2 (A), D304.2 (A), D310.2 (A), D311.1 (K), J401.2 (Ext), J402.2 (Ext), J403.S, R1.2, R3.2, R6.2, R8.2, R10.2, R12.2, R15.2, R17.2, R303.2, R305.2, R306.2, R309.2, RV1.3, RV2.3, T1.3 (SA), T2.3 (SA)
unnamed: C1.1, RV1.2
unnamed: C1.2, R1.1, R2.1
unnamed: C2.1, R3.1, SW2.1 (A), U1.8 (K)
unnamed: C3.1, SW2.2 (B)
unnamed: C4.1, R4.1, R5.1
unnamed: C5.1, R4.2, U1.6 (A)
unnamed: C5.2, R6.1, R7.1
unnamed: C6.1, R8.1, U2.3 (K_G3)
unnamed: C7.1, RV2.2
unnamed: C7.2, R10.1, R11.1
unnamed: C8.1, R13.1, R14.1
unnamed: C9.1, R12.1, SW3.1 (A), U3.8 (K)
unnamed: C10.1, SW3.2 (B)
unnamed: C11.1, R13.2, U3.6 (A)
unnamed: C11.2, R15.1, R16.1
unnamed: C12.1, R17.1, U4.3 (K_G3)
unnamed: C301.1, R302.2
unnamed: C301.2, D302.2 (A), D304.1 (K), T301.4 (SB)
unnamed: C302.1, D301.1 (K), D302.1 (K), L1.1
unnamed: C303.1, K1.12, L1.2, R5.2, R14.2, R303.1, R304.1, T1.1 (AA), T2.1 (AA)
unnamed: C304.1, C305.2, C306.2, C307.2, C308.1, D305.2 (A), D308.2 (A), D309.2 (A), K1.A2, R304.2, R305.1, R308.2, U1.9 (F2), U2.5 (F2), U202.5 (F2)
unnamed: C305.1, C306.1, D305.1 (K), D306.1 (K), D307.1 (K), K1.A1, U301.3 (VI)
unnamed: C307.1, R307.2, R308.1, U301.1 (ADJ)
unnamed: C308.2, R307.1, U1.4 (F1), U1.5 (F1), U2.4 (F1), U202.4 (F1), U301.2 (VO)
unnamed: C309.1, D310.1 (K), D311.2 (A), J1.3, R309.1
unnamed: C401.1, J401.1 (In), R401.1, R407.1
unnamed: C401.2, R401.2, RV1.1, SW401.5 (B)
unnamed: C404.2, R404.2, R406.1
unnamed: C405.2, R407.2, R409.1
unnamed: C406.1, J402.1 (In), R404.1, R408.1
unnamed: C406.2, R408.2, RV2.1, SW402.5 (B)
unnamed: D301.2 (A), D303.1 (K), R302.1, T301.3 (SA)
unnamed: D306.2 (A), D308.1 (K), T301.5 (SC)
unnamed: D307.2 (A), D309.1 (K), T301.6 (SD)
unnamed: F1.1, J1.1
unnamed: F1.2, SW1.1 (A)
unnamed: J1.2, SW1.3 (A)
unnamed: J403.R, T2.4 (SB)
unnamed: J403.T, T1.4 (SB)
unnamed: K1.11, R306.1
unnamed: NE1.1, RV301.2, SW1.4 (B), T301.2 (AB)
unnamed: NE1.2, R301.2
unnamed: R2.2, U1.7 (G)
unnamed: R7.2, U2.2 (G1)
unnamed: R9.1, T1.2 (AB), U2.7 (A)
unnamed: R9.2, U2.9 (G2)
unnamed: R11.2, U3.7 (G)
unnamed: R16.2, U4.2 (G1)
unnamed: R18.1, T2.2 (AB), U4.7 (A)
unnamed: R18.2, U4.9 (G2)
unnamed: R301.1, RT1.2, RV301.1, T301.1 (AA)
unnamed: R406.2, SW401.4 (A)
unnamed: R409.2, SW402.4 (A)
unnamed: RT1.1, SW1.2 (B)

Notes on the sheet:
ZASILACZ B+ 300V (CLC) + rozladowanie K1
WEJSCIE: gniazda RCA, crossfeed S1, glosnosc RV1
KANAL P: 1/2 ECC82 -> EL84 (trioda) -> OPT
SIEC 230V + ground breaker
L1 = dlawik zasilacza (nie mylic z Lp OPT >=25H - patrz T1/T201)
UWAGA: napiecia do ok. 330V DC - smiertelnie niebezpieczne. Po wylaczeniu odczekac na
LD1085 (LDO) - LM317 ma za duzy dropout przy 1,7A (V_RAW ~9V z uzwojenia 7V wystarcza).
S1 crossfeed: ON = przesluch -14 dB w basie (<700 Hz), OFF = tor prosty
PE -> wlasna sruba M4 na chassis
ZARZENIE 6,3V DC (LD1085, elewacja ELEV)
Skrecona para na przewodach zarzenia. LD1085: blaszka = VOUT - izolacja od chassis.
Ground breaker (jedyny styk masy z chassis): 10R przerywa petle masy;
Zarzenie do lamp: skrecona para, minus = ELEV (+53V).
-> B+ <50V w ok. 15 s. K1: cewka 9V (V_RAW), styki min. 250V. Bleeder R303 = wolna 2. linia.
7V/3A (zarzenie)
przy usterce diody zwieraja GND do PE i bezpiecznik zadziala.
KANAL L: 1/2 ECC82 -> EL84 (trioda) -> OPT
Zarzenie: 6,3V DC / ok. 1,7A (2x EL84 0,76A + ECC82 0,15A; budzet 1,9A) z uzwojenia 7V/3A.
WYJSCIE: jack 6,3 mm
Rozladowanie: przy zaniku sieci K1 zwalnia, styk NC (11-12) laczy +300V z R306
230V/0,15A (HT)
rozladowanie (K1) i SPRAWDZIC woltomierzem KAZDA sekcje (<50V) przed praca.
